bbenchoff/Dumb-Badge/Art-Assets/Documentation/CodePage437.png

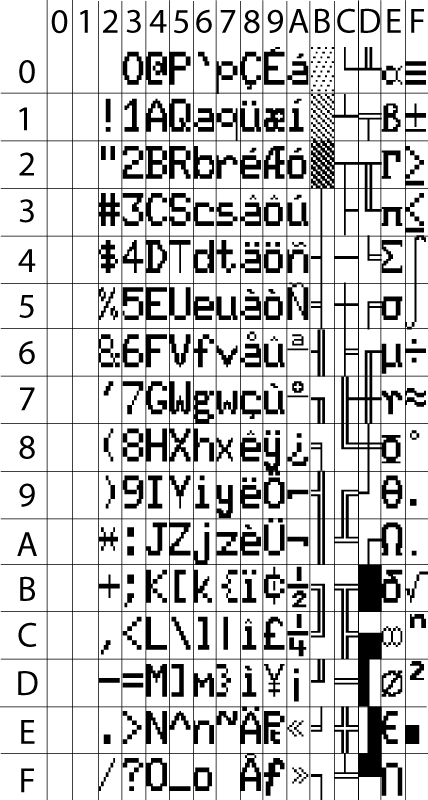
Art-Assets/Documentation/CodePage437.png
