bbenchoff/Dumb-Badge/Art-Assets/Documentation/GraphicRenditionDataStructure.png

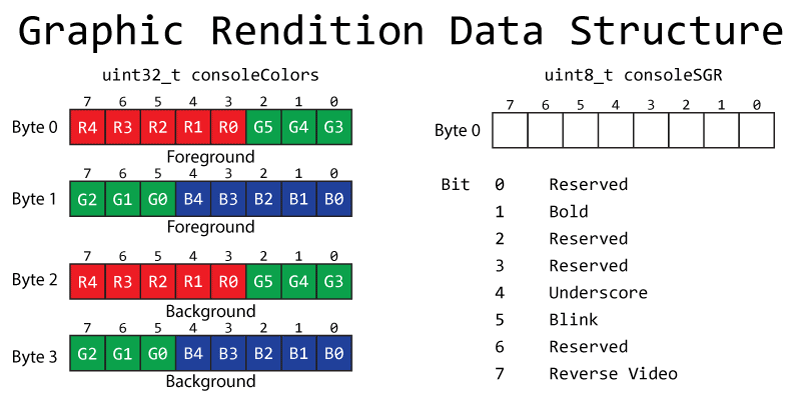
Art-Assets/Documentation/GraphicRenditionDataStructure.png
