bbenchoff/Dumb-Badge/Art-Assets/Documentation/PiHeader.png

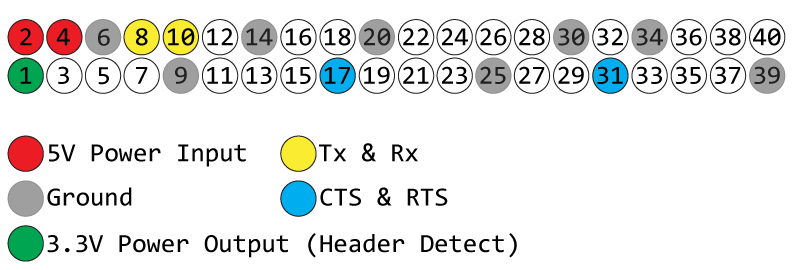
Art-Assets/Documentation/PiHeader.png
