bbenchoff/Dumb-Badge/Art-Assets/Documentation/StateMachine.png

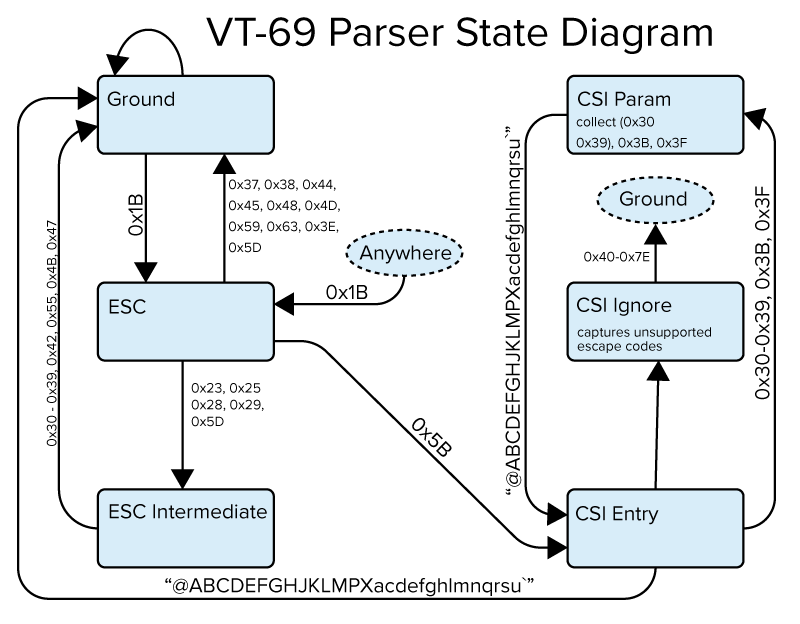
Art-Assets/Documentation/StateMachine.png
