bbenchoff/Dumb-Badge/Art-Assets/Font/CodePage_437.bmp

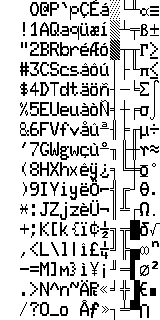
Art-Assets/Font/CodePage_437.bmp
