bbenchoff/Dumb-Badge/Art-Assets/Large Render.png

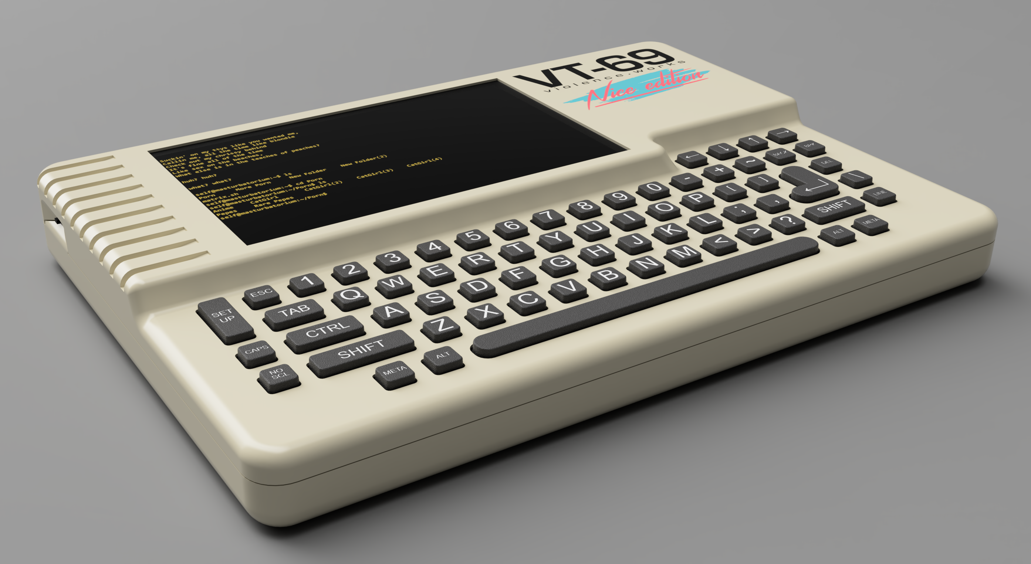
Art-Assets/Large Render.png
