bbenchoff/Dumb-Badge/Art-Assets/Model Decals/ClearConsole.png

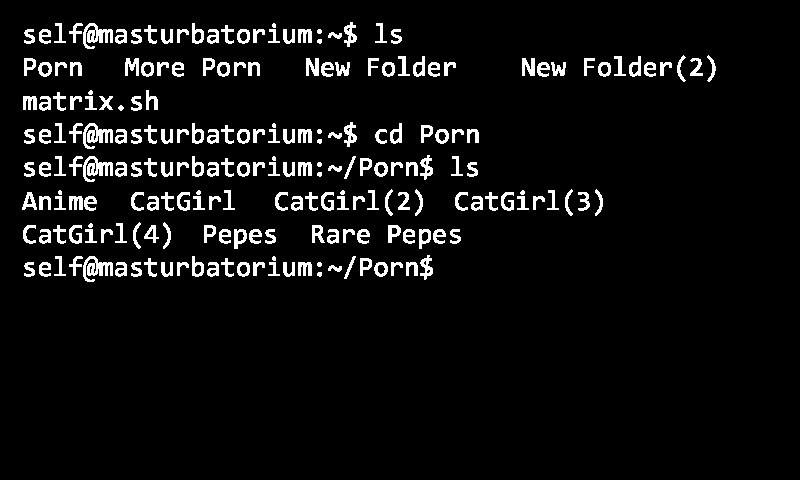
Art-Assets/Model Decals/ClearConsole.png
