bbenchoff/Dumb-Badge/Art-Assets/Model Decals/ClearConsole_flipped.png

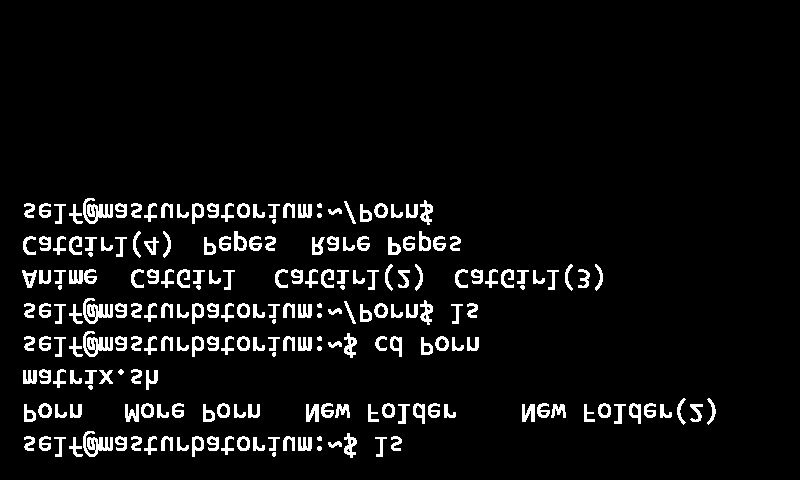
Art-Assets/Model Decals/ClearConsole_flipped.png
