bbenchoff/Dumb-Badge/Art-Assets/Model Decals/Console.png

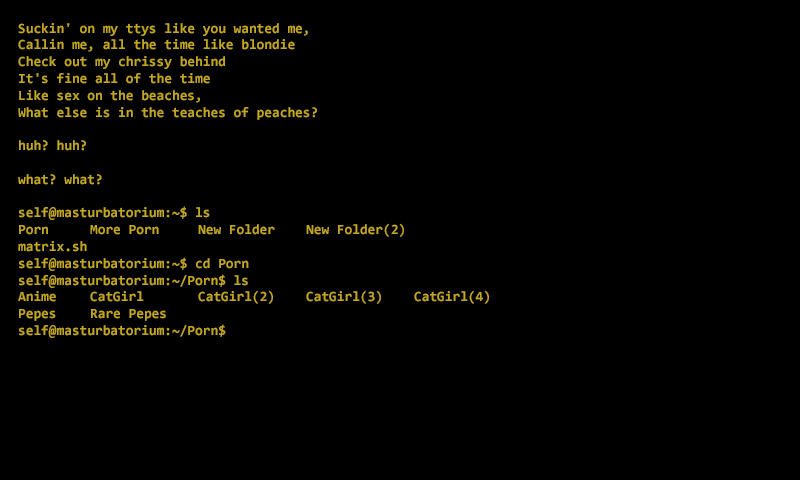
Art-Assets/Model Decals/Console.png
