bbenchoff/Dumb-Badge/Art-Assets/Model Decals/Console_flipped.png

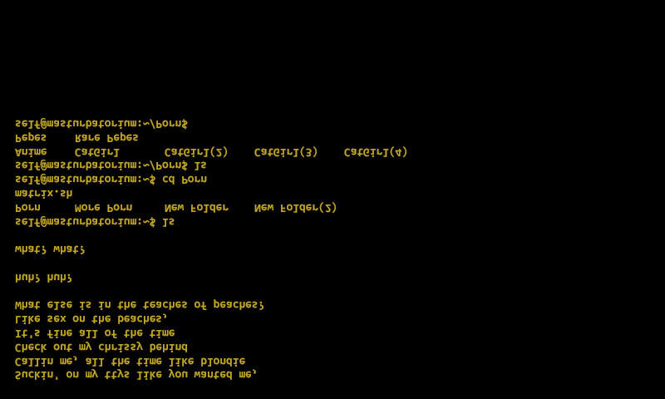
Art-Assets/Model Decals/Console_flipped.png
