bbenchoff/Dumb-Badge/Art-Assets/Model Decals/ConsoleGreen.png

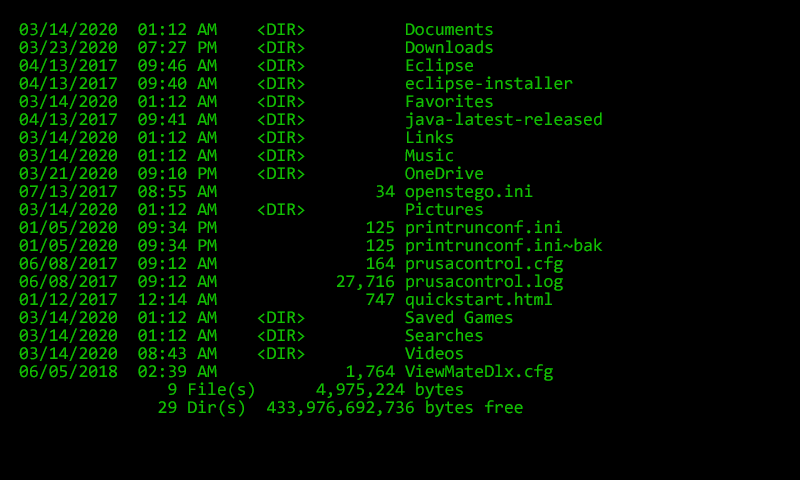
Art-Assets/Model Decals/ConsoleGreen.png
