bbenchoff/Dumb-Badge/Art-Assets/Model Decals/ConsoleGreen_flipped.png

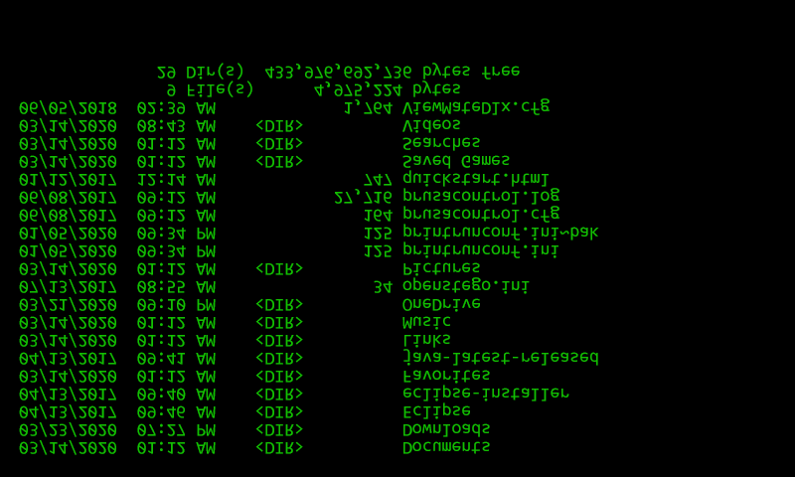
Art-Assets/Model Decals/ConsoleGreen_flipped.png
