bbenchoff/Dumb-Badge/Art-Assets/Model Decals/ConsoleWhite.png

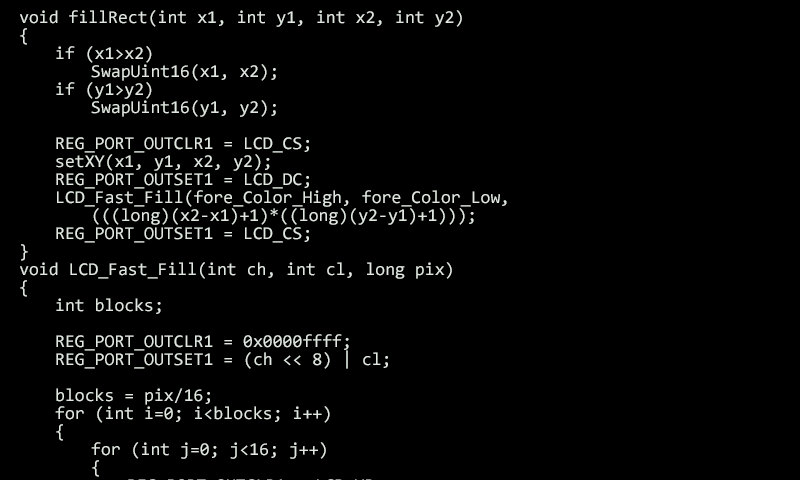
Art-Assets/Model Decals/ConsoleWhite.png
