bbenchoff/Dumb-Badge/Art-Assets/Model Decals/ConsoleWhite_flipped.png

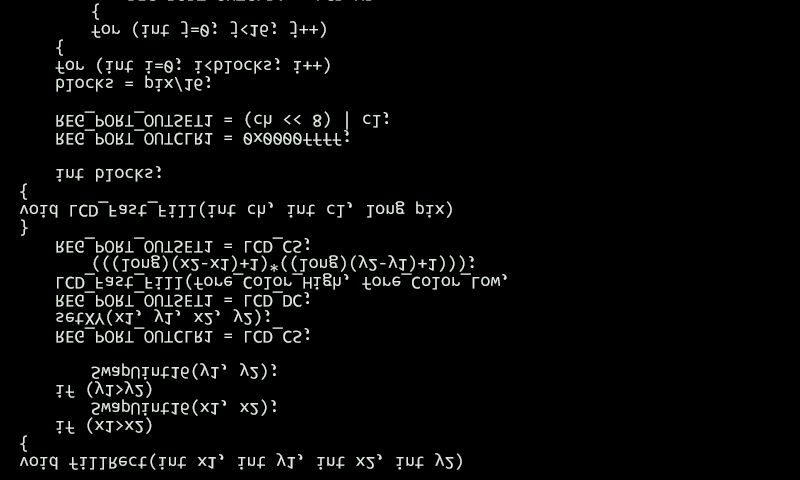
Art-Assets/Model Decals/ConsoleWhite_flipped.png
