bbenchoff/Dumb-Badge/Art-Assets/Model Decals/NiceEdition.png

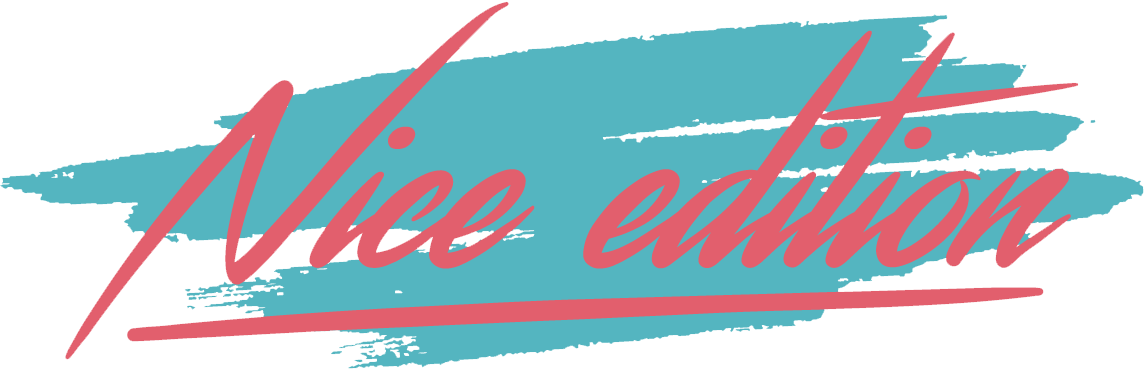
Art-Assets/Model Decals/NiceEdition.png
