bbenchoff/Dumb-Badge/Art-Assets/Model Decals/NiceEdition_flipped.png

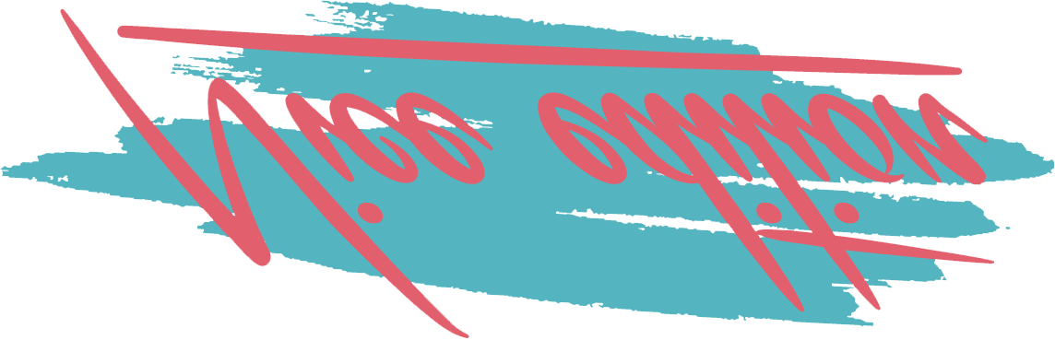
Art-Assets/Model Decals/NiceEdition_flipped.png
