bbenchoff/Dumb-Badge/Art-Assets/Model Decals/TechNews.png

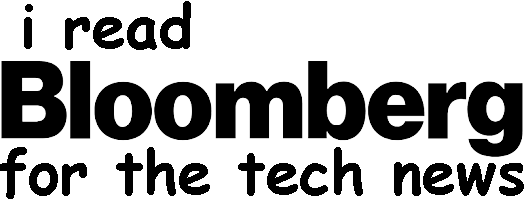
Art-Assets/Model Decals/TechNews.png
