bbenchoff/Dumb-Badge/Art-Assets/Model Decals/TechNews_flipped.png

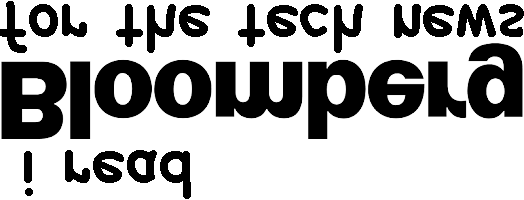
Art-Assets/Model Decals/TechNews_flipped.png
