bbenchoff/Dumb-Badge/Art-Assets/Model Decals/Transparent.png

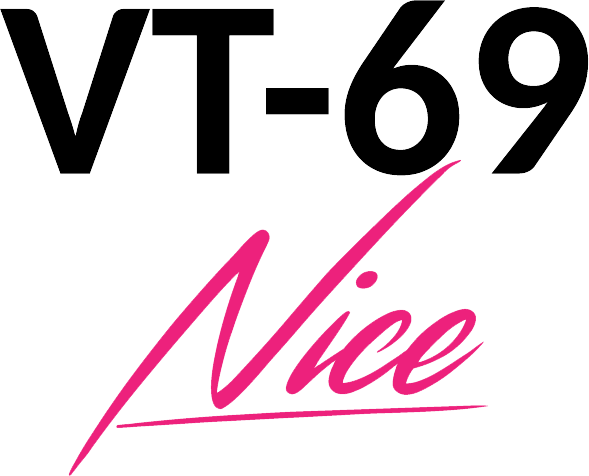
Art-Assets/Model Decals/Transparent.png
