bbenchoff/Dumb-Badge/Art-Assets/Model Decals/VT69Decal.png

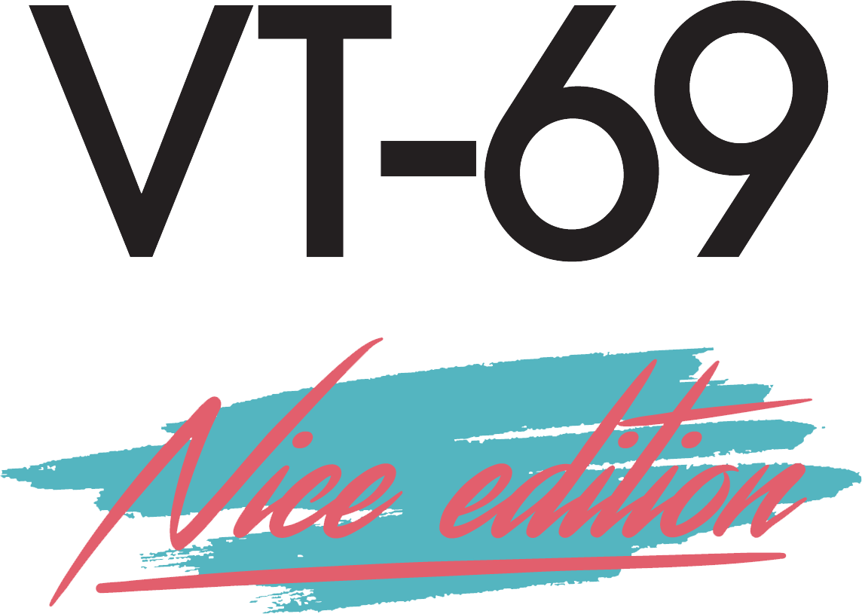
Art-Assets/Model Decals/VT69Decal.png
