bbenchoff/Dumb-Badge/Art-Assets/Model Decals/VT69Decal_flipped.png

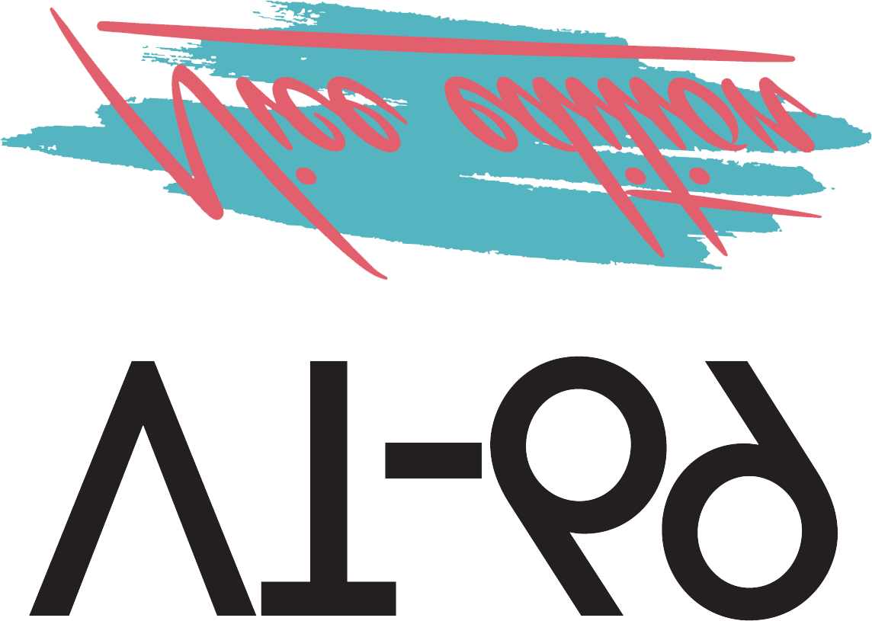
Art-Assets/Model Decals/VT69Decal_flipped.png
