bbenchoff/Dumb-Badge/Art-Assets/Model Decals/VT69DumbTerm.png

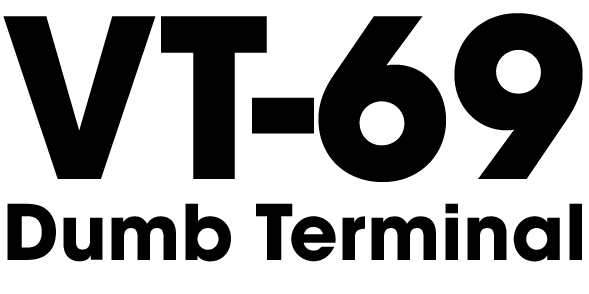
Art-Assets/Model Decals/VT69DumbTerm.png
