bbenchoff/Dumb-Badge/Art-Assets/Model Decals/VT69DumbTerm_flipped.png

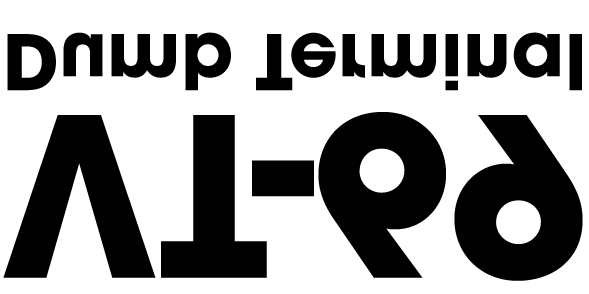
Art-Assets/Model Decals/VT69DumbTerm_flipped.png
