bbenchoff/Dumb-Badge/Art-Assets/Model Decals/VT69DumbTermInverse.png

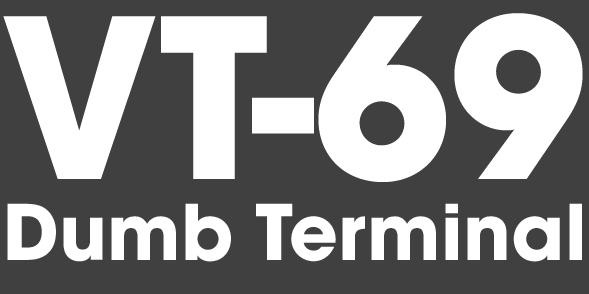
Art-Assets/Model Decals/VT69DumbTermInverse.png
