bbenchoff/Dumb-Badge/Art-Assets/Model Decals/VT69DumbTermInverse_flipped.png

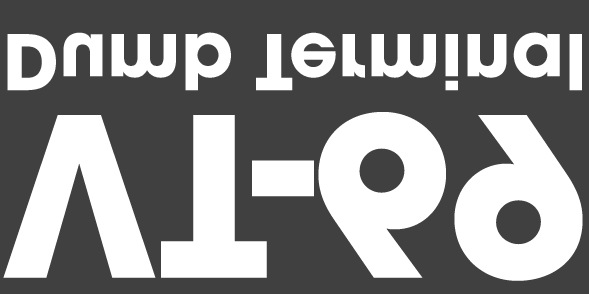
Art-Assets/Model Decals/VT69DumbTermInverse_flipped.png
