bbenchoff/Dumb-Badge/Art-Assets/Model Decals/VT69DumbTermWhite.png

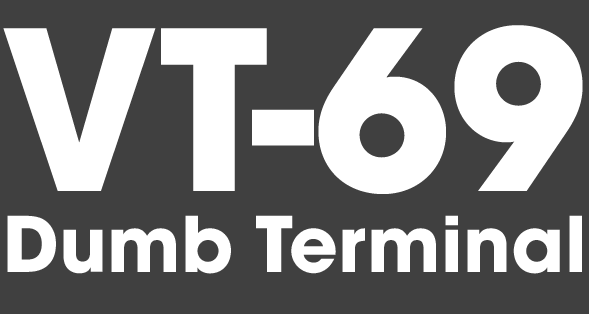
Art-Assets/Model Decals/VT69DumbTermWhite.png
