bbenchoff/Dumb-Badge/Art-Assets/Model Decals/VT69DumbTermWhite_flipped.png

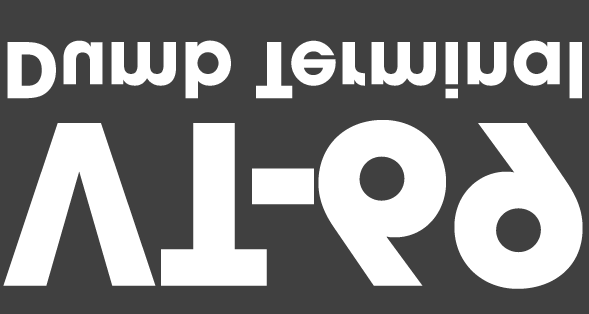
Art-Assets/Model Decals/VT69DumbTermWhite_flipped.png
