bbenchoff/Dumb-Badge/Art-Assets/Model Decals/VT69Nice.png

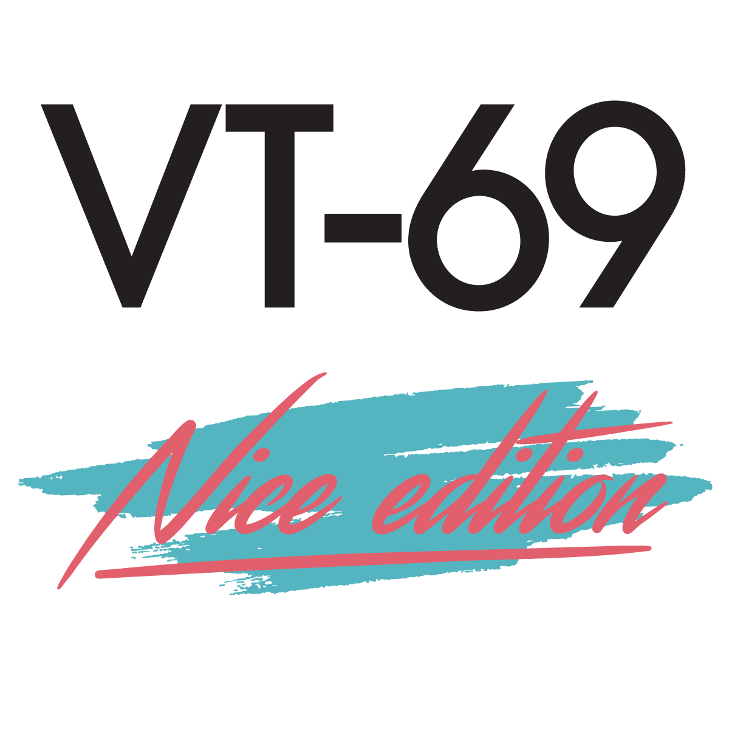
Art-Assets/Model Decals/VT69Nice.png
