bbenchoff/Dumb-Badge/Art-Assets/Model Decals/VT69NiceEditionLong.png

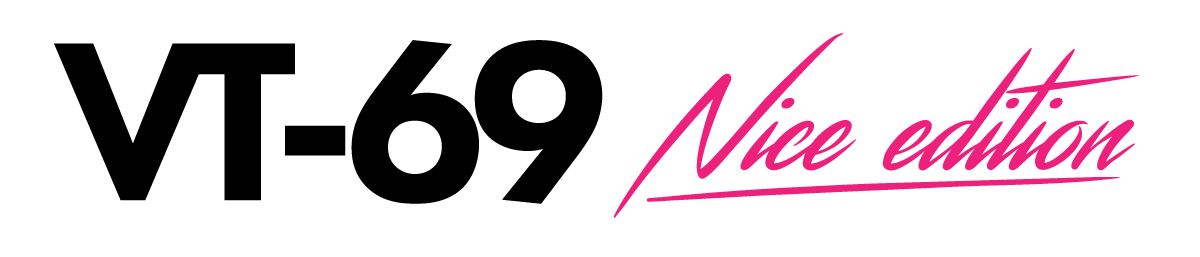
Art-Assets/Model Decals/VT69NiceEditionLong.png
