bbenchoff/Dumb-Badge/Art-Assets/Model Decals/VT69NiceEditionLongTall.png

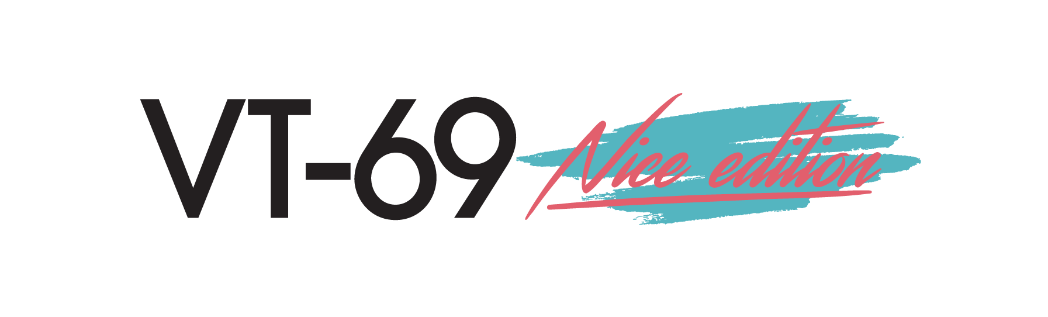
Art-Assets/Model Decals/VT69NiceEditionLongTall.png
