bbenchoff/Dumb-Badge/Art-Assets/Model Decals/VT69NiceEurostyle.png

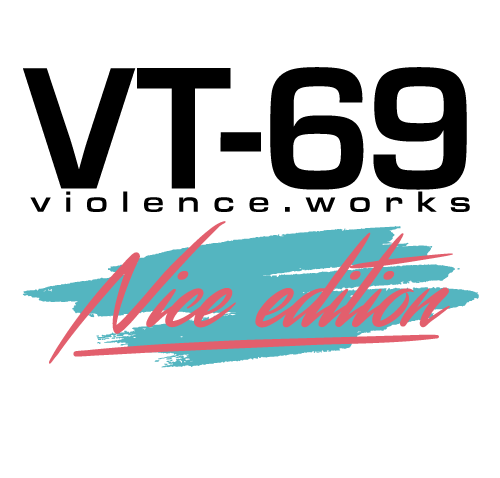
Art-Assets/Model Decals/VT69NiceEurostyle.png
