bbenchoff/Dumb-Badge/Art-Assets/Model Decals/VT69NiceEurostyle_flipped.png

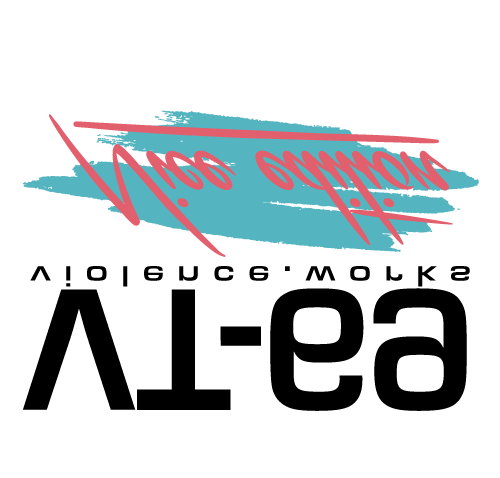
Art-Assets/Model Decals/VT69NiceEurostyle_flipped.png
