bbenchoff/Dumb-Badge/Art-Assets/Model Decals/VT69NiceSquare.png

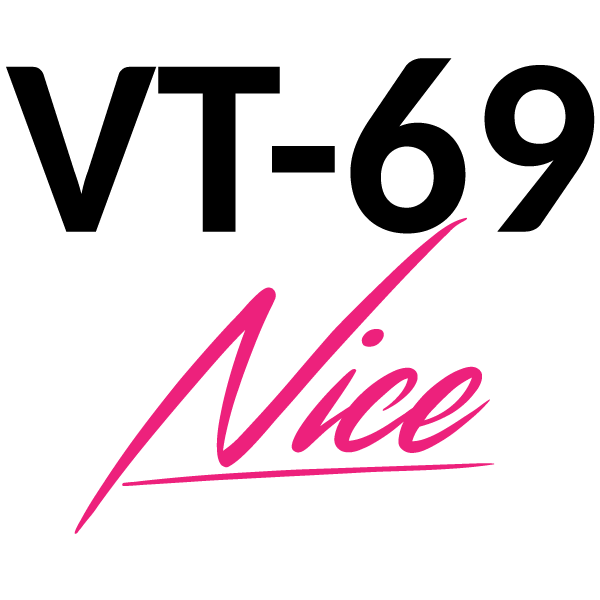
Art-Assets/Model Decals/VT69NiceSquare.png
