bbenchoff/Dumb-Badge/Art-Assets/RandomGraphics/ComfortablyDumb.png

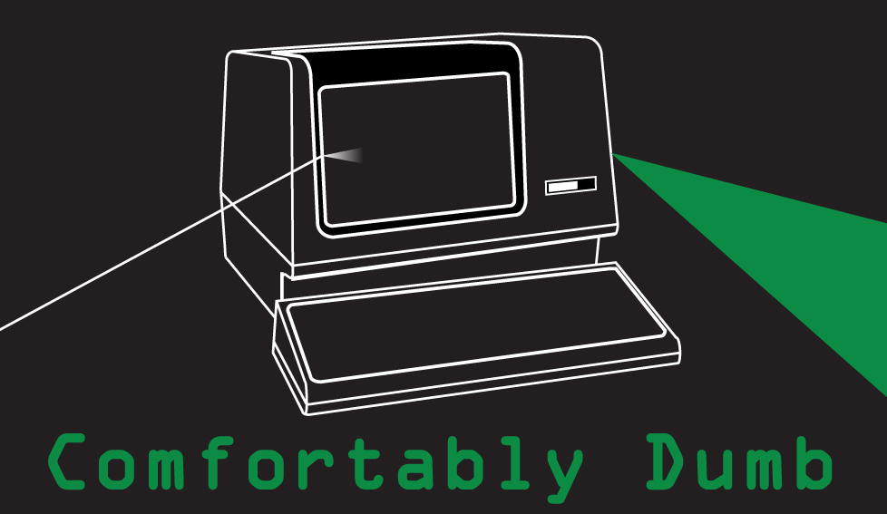
Art-Assets/RandomGraphics/ComfortablyDumb.png
