bbenchoff/Dumb-Badge/Art-Assets/RandomGraphics/Dick S/DickSPNG.png

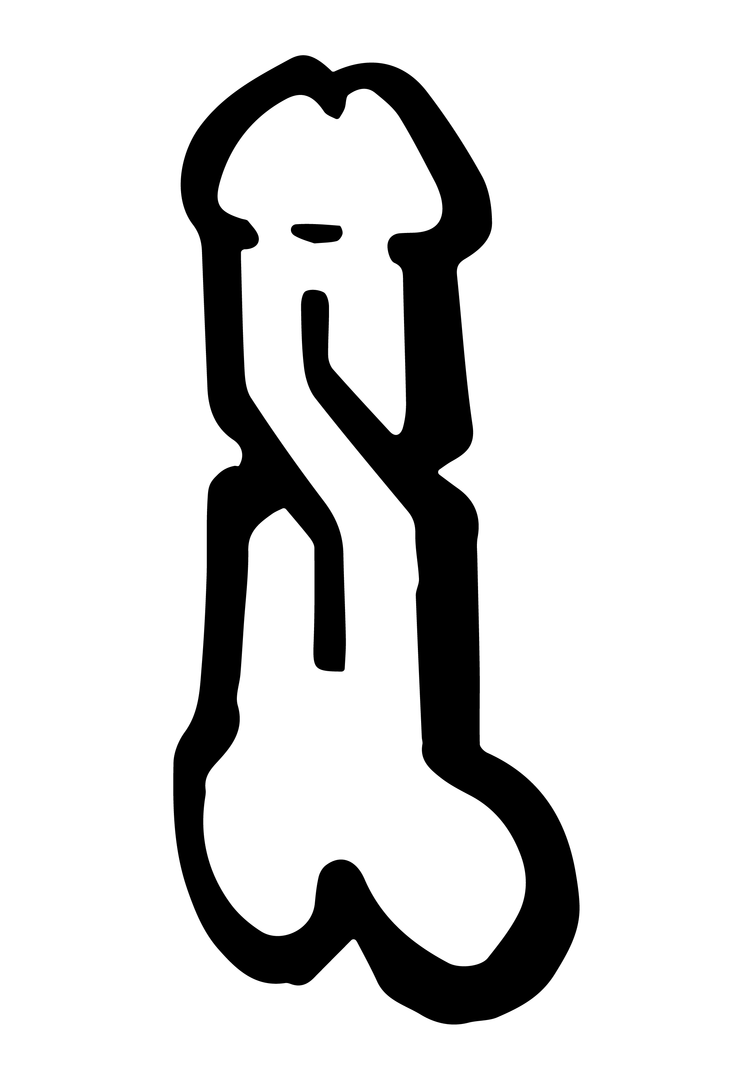
Art-Assets/RandomGraphics/Dick S/DickSPNG.png
