bbenchoff/Dumb-Badge/Art-Assets/RandomGraphics/KillAllTheWhiteMan/KillAll800x480.png

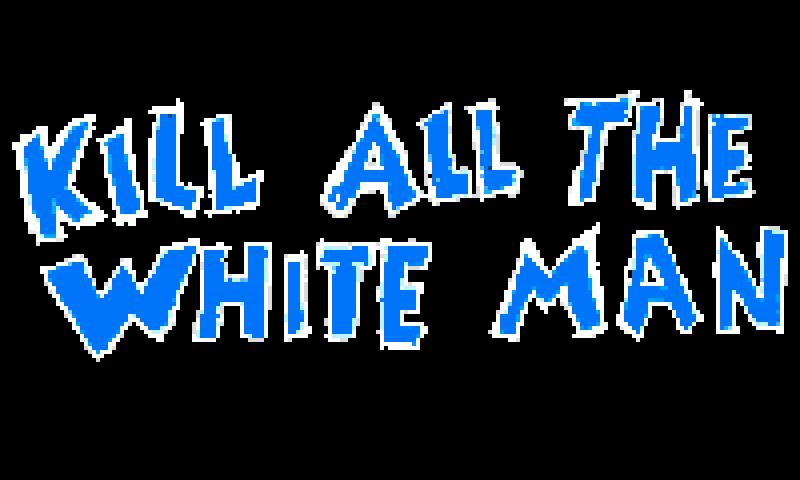
Art-Assets/RandomGraphics/KillAllTheWhiteMan/KillAll800x480.png
