bbenchoff/Dumb-Badge/Art-Assets/RandomGraphics/KillAllTheWhiteMan/KillAll.png

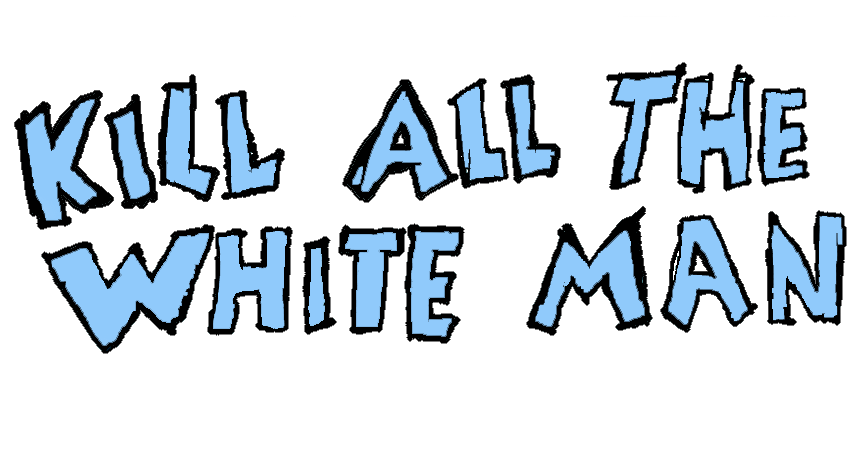
Art-Assets/RandomGraphics/KillAllTheWhiteMan/KillAll.png
