bbenchoff/Dumb-Badge/Art-Assets/RandomGraphics/MechDrawing/Drawing.png

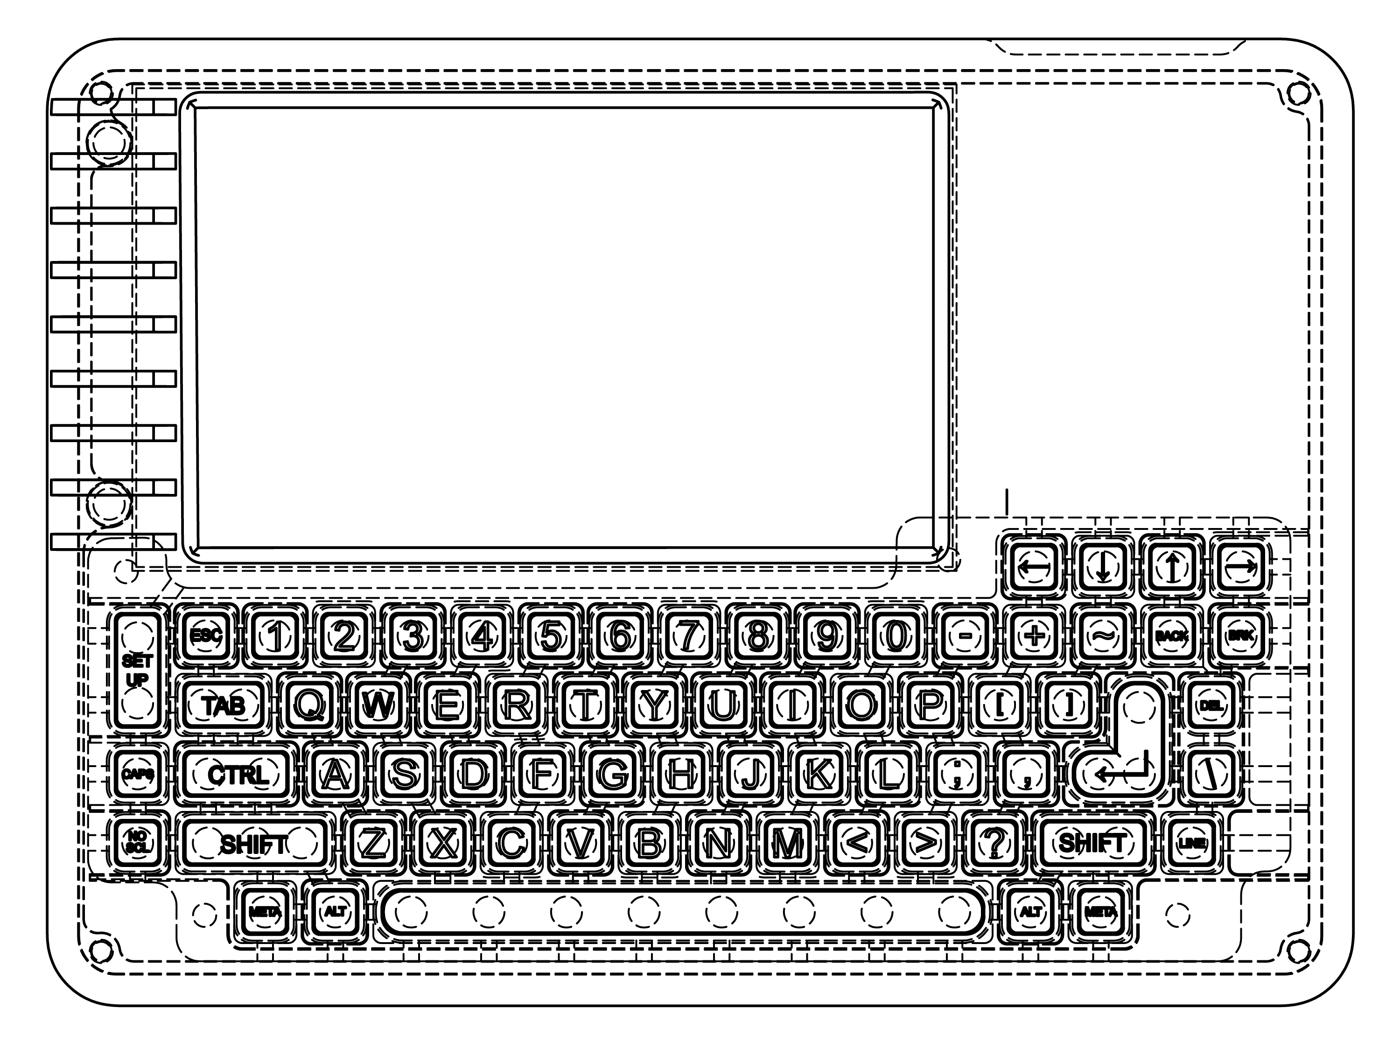
Art-Assets/RandomGraphics/MechDrawing/Drawing.png
