bbenchoff/Dumb-Badge/Art-Assets/RandomGraphics/MechDrawing/DrawingInvert.png

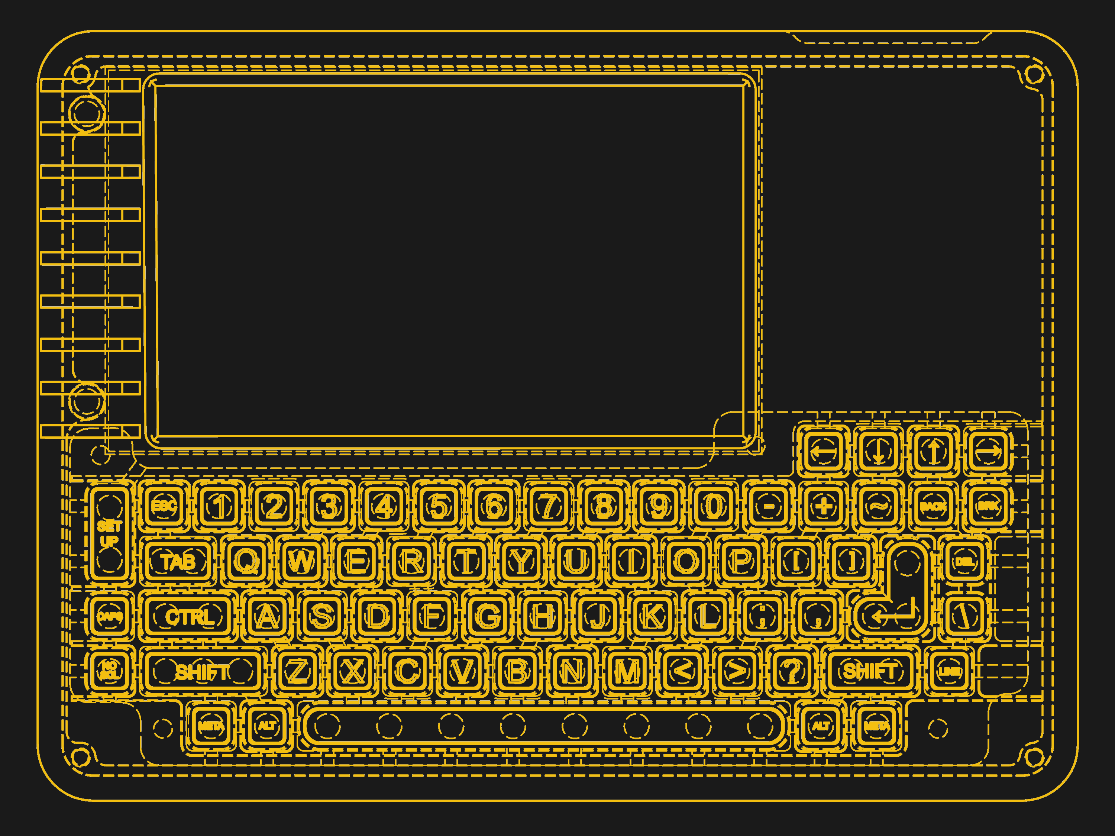
Art-Assets/RandomGraphics/MechDrawing/DrawingInvert.png
