bbenchoff/Dumb-Badge/Art-Assets/RandomGraphics/MechDrawing/YellowTransparentMechDrawing.png

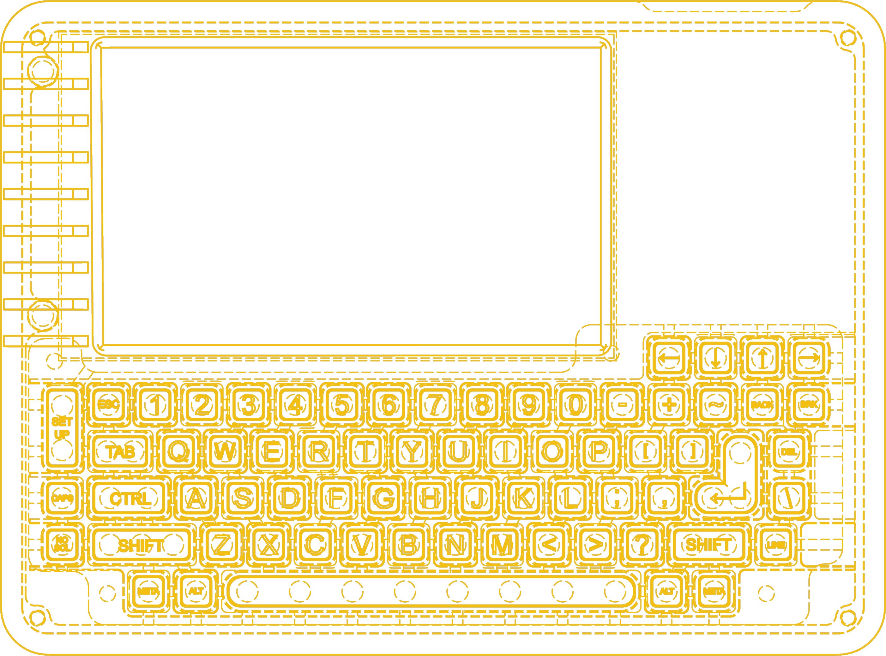
Art-Assets/RandomGraphics/MechDrawing/YellowTransparentMechDrawing.png
