bbenchoff/Dumb-Badge/Art-Assets/RandomGraphics/NiceTTYs/NiceTTYs.png

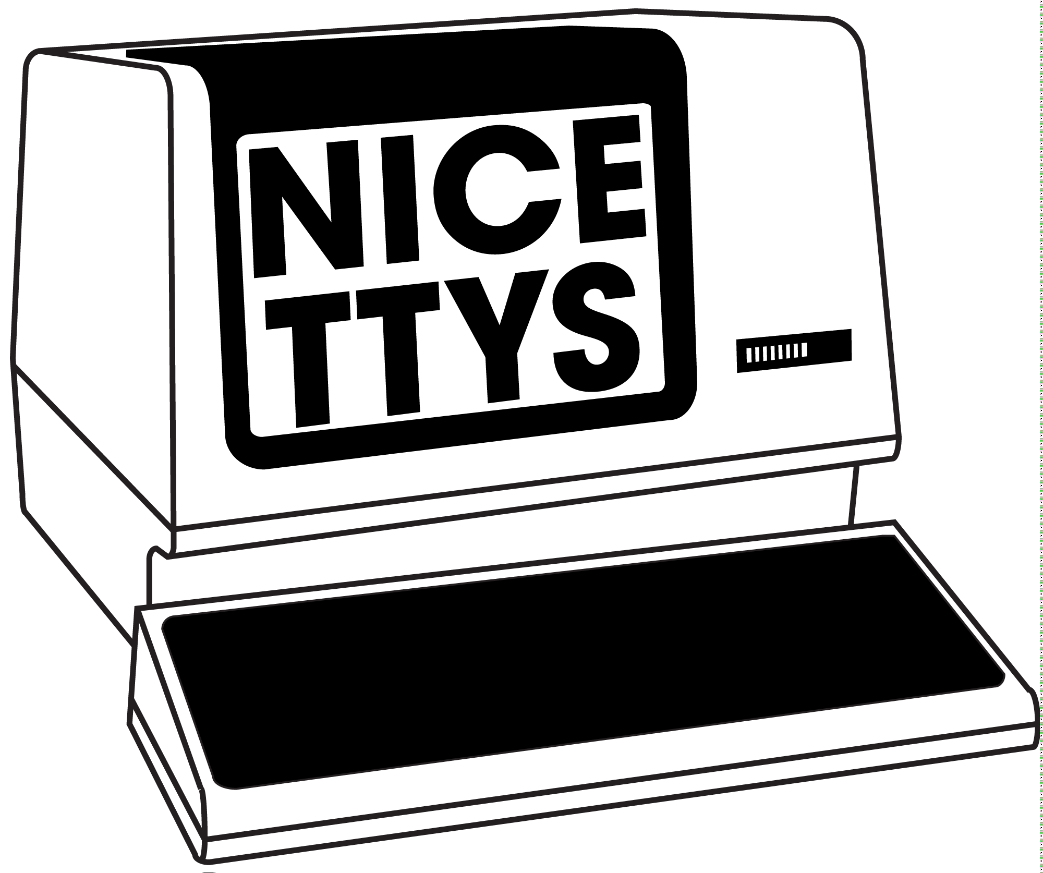
Art-Assets/RandomGraphics/NiceTTYs/NiceTTYs.png
