bbenchoff/Dumb-Badge/Art-Assets/RandomGraphics/reference/Album Covers where guitars are spaceships/51t4X-C2m3L.jpg

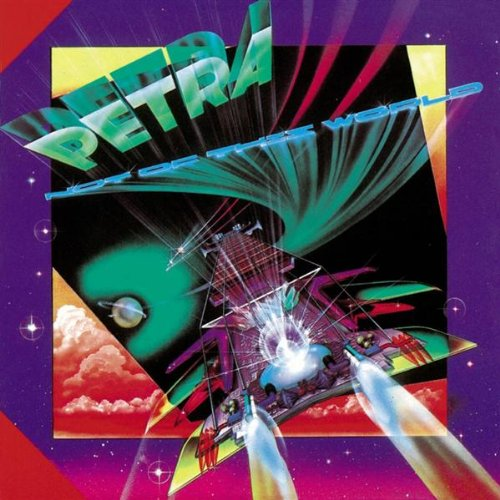
Art-Assets/RandomGraphics/reference/Album Covers where guitars are spaceships/51t4X-C2m3L.jpg
