bbenchoff/Dumb-Badge/Art-Assets/RandomGraphics/reference/Album Covers where guitars are spaceships/740739_10151165755966707_379962912_o.jpg

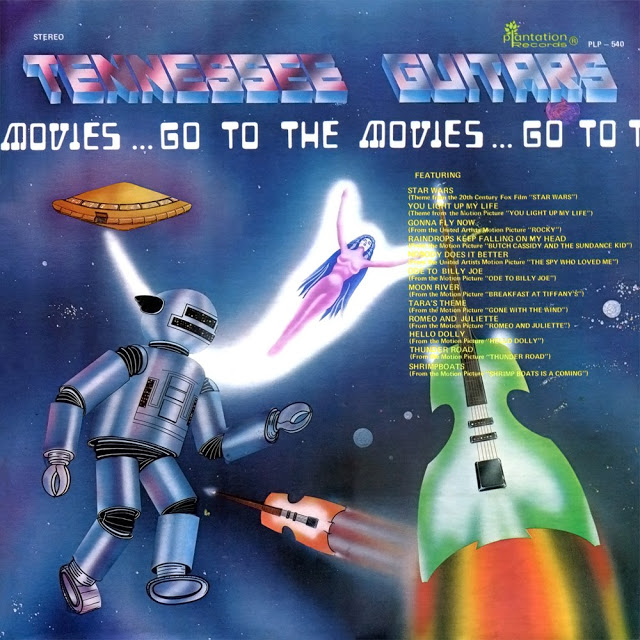
Art-Assets/RandomGraphics/reference/Album Covers where guitars are spaceships/740739_10151165755966707_379962912_o.jpg
