bbenchoff/Dumb-Badge/Art-Assets/RandomGraphics/reference/Album Covers where guitars are spaceships/cbf672cb8266beb2027a6619fb71dfe7.1000x1000x1.jpg

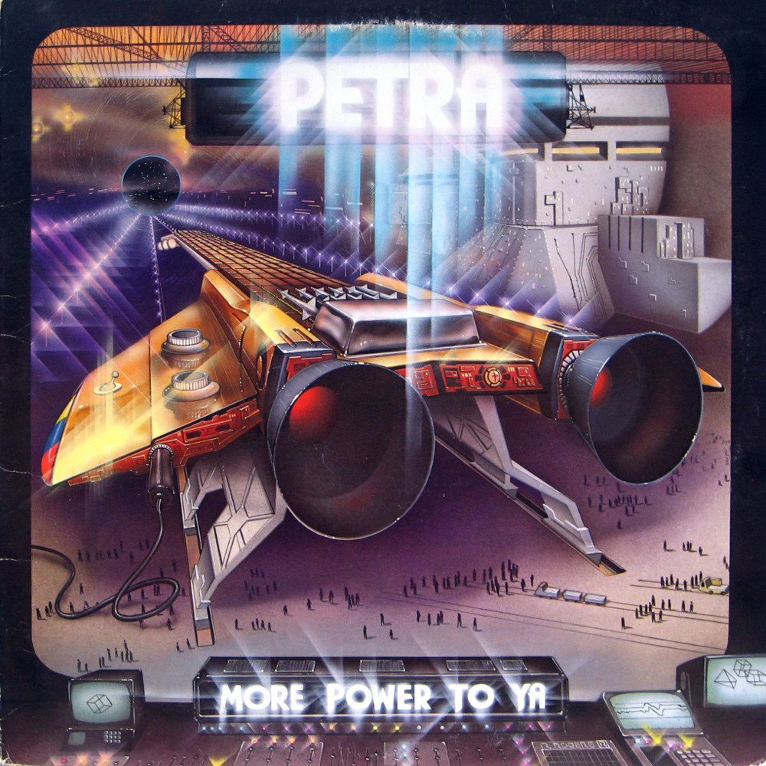
Art-Assets/RandomGraphics/reference/Album Covers where guitars are spaceships/cbf672cb8266beb2027a6619fb71dfe7.1000x1000x1.jpg
