bbenchoff/Dumb-Badge/Art-Assets/RandomGraphics/reference/Album Covers where guitars are spaceships/CNINJA.jpg

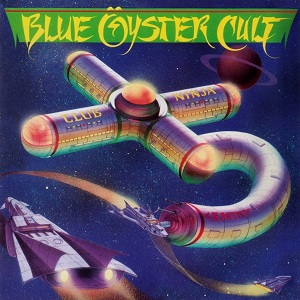
Art-Assets/RandomGraphics/reference/Album Covers where guitars are spaceships/CNINJA.jpg
