bbenchoff/Dumb-Badge/Art-Assets/RandomGraphics/reference/Album Covers where guitars are spaceships/MI0000687644.jpg

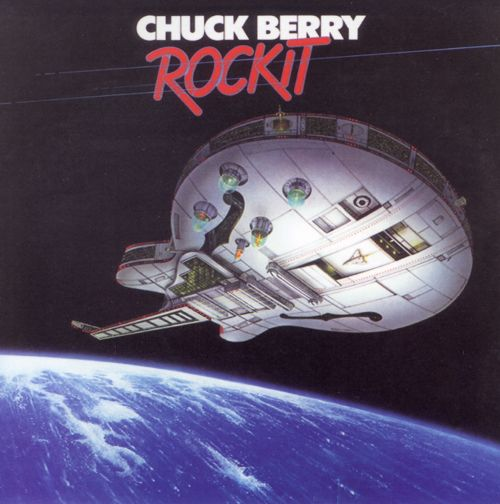
Art-Assets/RandomGraphics/reference/Album Covers where guitars are spaceships/MI0000687644.jpg
