bbenchoff/Dumb-Badge/Art-Assets/RandomGraphics/reference/Album Covers where guitars are spaceships/MI0001766384.jpg

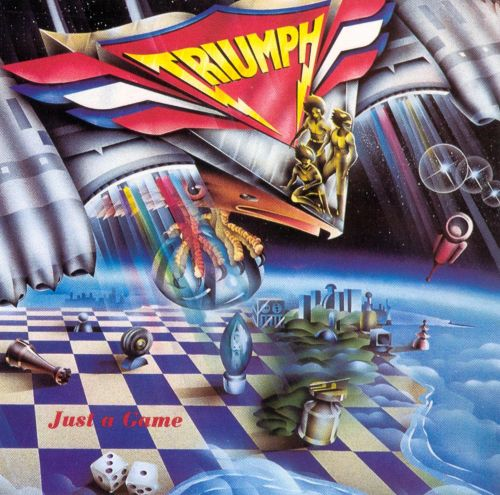
Art-Assets/RandomGraphics/reference/Album Covers where guitars are spaceships/MI0001766384.jpg
