bbenchoff/Dumb-Badge/Art-Assets/RandomGraphics/reference/Album Covers where guitars are spaceships/quartz-against-all-odds-20180325070727.jpg

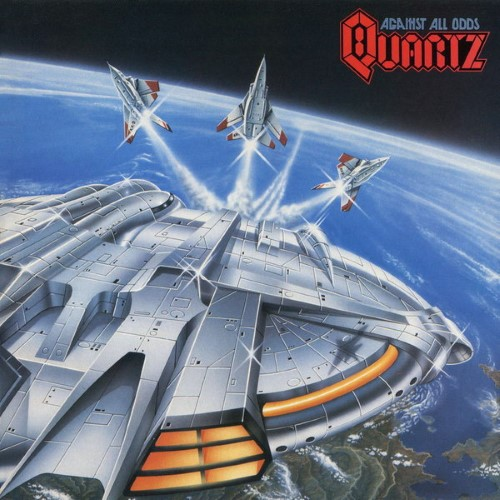
Art-Assets/RandomGraphics/reference/Album Covers where guitars are spaceships/quartz-against-all-odds-20180325070727.jpg
