bbenchoff/Dumb-Badge/Art-Assets/RandomGraphics/reference/Album Covers where guitars are spaceships/R-342681-1356796270-8952.jpeg.jpg

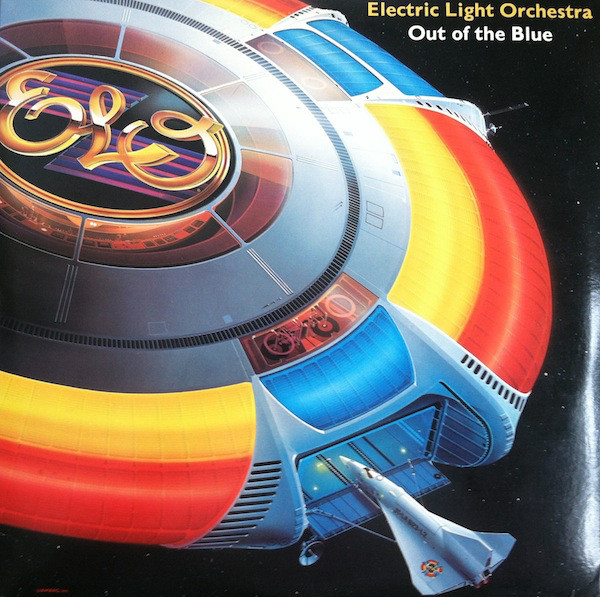
Art-Assets/RandomGraphics/reference/Album Covers where guitars are spaceships/R-342681-1356796270-8952.jpeg.jpg
