bbenchoff/Dumb-Badge/Art-Assets/RandomGraphics/reference/Album Covers where guitars are spaceships/R-543205-1365450873-9314.jpeg.jpg

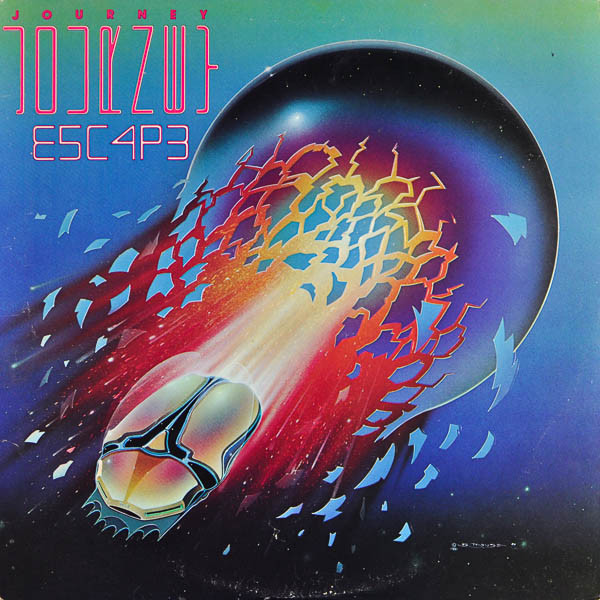
Art-Assets/RandomGraphics/reference/Album Covers where guitars are spaceships/R-543205-1365450873-9314.jpeg.jpg
