bbenchoff/Dumb-Badge/Art-Assets/RandomGraphics/reference/Album Covers where guitars are spaceships/R-1697630-1237652205.jpeg.jpg

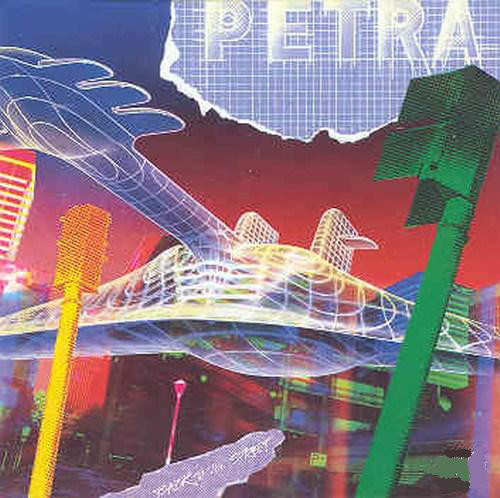
Art-Assets/RandomGraphics/reference/Album Covers where guitars are spaceships/R-1697630-1237652205.jpeg.jpg
