bbenchoff/Dumb-Badge/Art-Assets/RandomGraphics/reference/Album Covers where guitars are spaceships/R-1715578-1274193568.jpeg.jpg

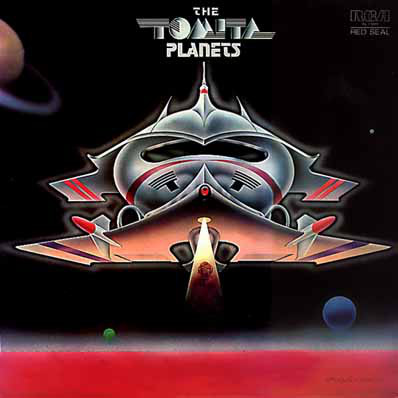
Art-Assets/RandomGraphics/reference/Album Covers where guitars are spaceships/R-1715578-1274193568.jpeg.jpg
