bbenchoff/Dumb-Badge/Art-Assets/RandomGraphics/SoloJazz/1.png

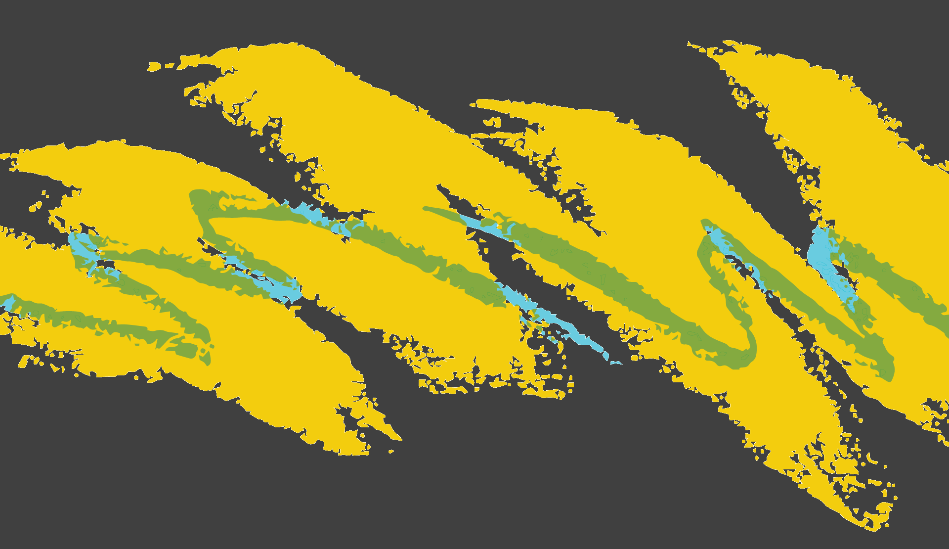
Art-Assets/RandomGraphics/SoloJazz/1.png
