bbenchoff/Dumb-Badge/Art-Assets/RandomGraphics/SoloJazz/2.png

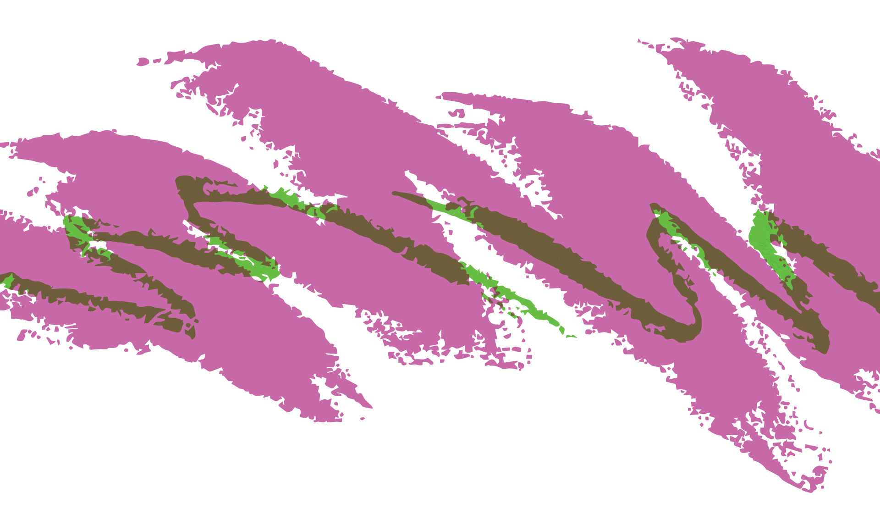
Art-Assets/RandomGraphics/SoloJazz/2.png
