bbenchoff/Dumb-Badge/Art-Assets/RandomGraphics/SoloJazz/lol-art.png

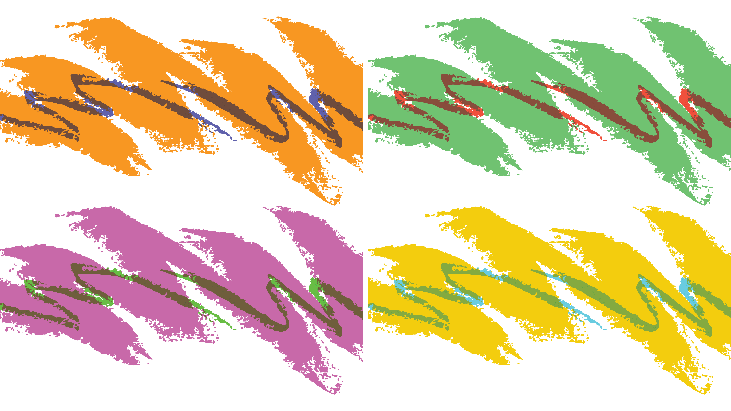
Art-Assets/RandomGraphics/SoloJazz/lol-art.png
