bbenchoff/Dumb-Badge/Art-Assets/RandomGraphics/SpiritOf89/SpiritOf89.png

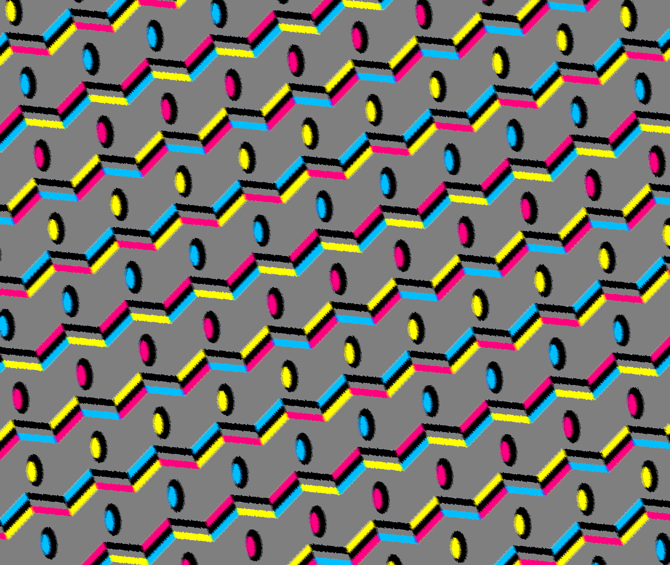
Art-Assets/RandomGraphics/SpiritOf89/SpiritOf89.png
