bbenchoff/Dumb-Badge/Art-Assets/RandomGraphics/SpiritOf89/SpiritOf89small.png

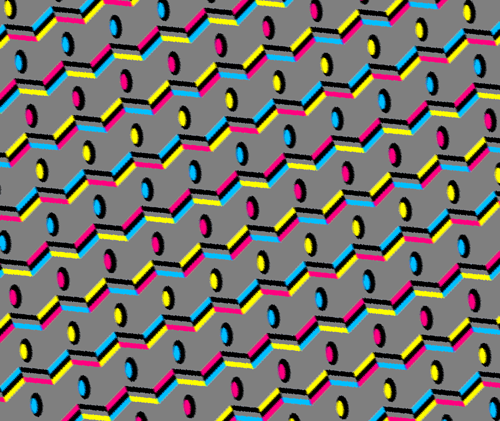
Art-Assets/RandomGraphics/SpiritOf89/SpiritOf89small.png
