bbenchoff/Dumb-Badge/Art-Assets/RandomGraphics/SusanKare/BigSadTerm.png

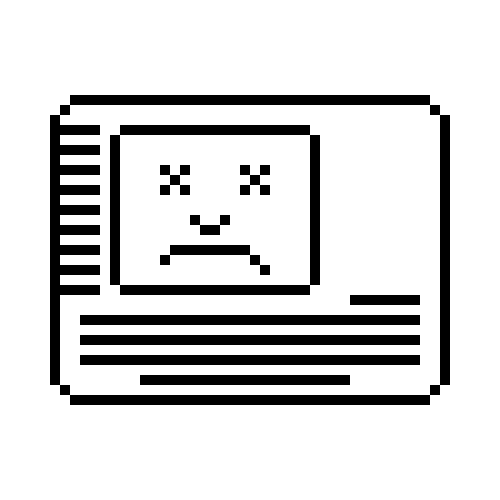
Art-Assets/RandomGraphics/SusanKare/BigSadTerm.png
