bbenchoff/Dumb-Badge/Art-Assets/RandomGraphics/SusanKare/BigVersion.png

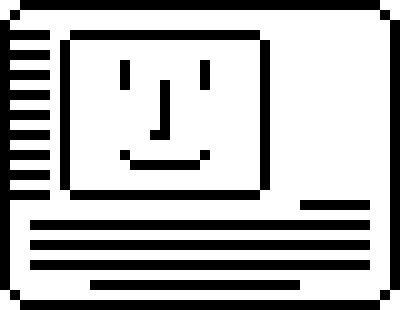
Art-Assets/RandomGraphics/SusanKare/BigVersion.png
