bbenchoff/Dumb-Badge/Art-Assets/RandomGraphics/SusanKare/SadTerm.png

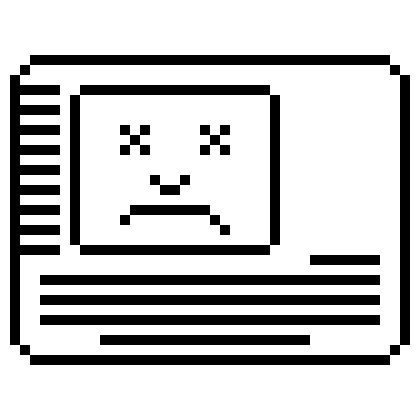
Art-Assets/RandomGraphics/SusanKare/SadTerm.png
