bbenchoff/Dumb-Badge/Art-Assets/RandomGraphics/Terminal/blankTerm.png

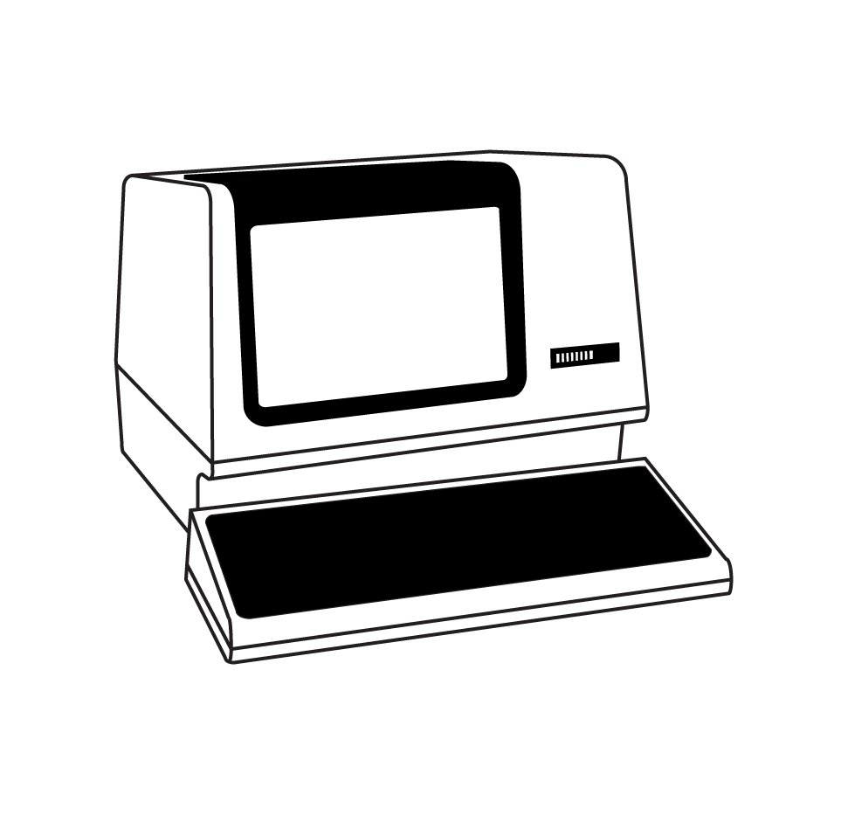
Art-Assets/RandomGraphics/Terminal/blankTerm.png
