bbenchoff/Dumb-Badge/Art-Assets/RandomGraphics/ToeJam/ToejamAndEarl.png

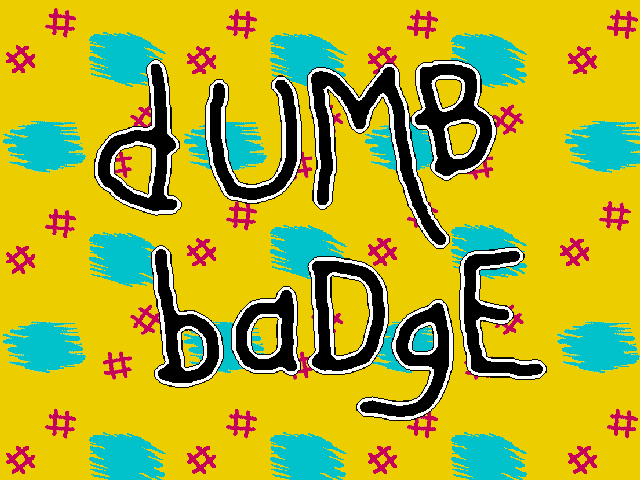
Art-Assets/RandomGraphics/ToeJam/ToejamAndEarl.png
