bbenchoff/Dumb-Badge/Art-Assets/RandomGraphics/ToeJam/ToejamAndEarlWide.png

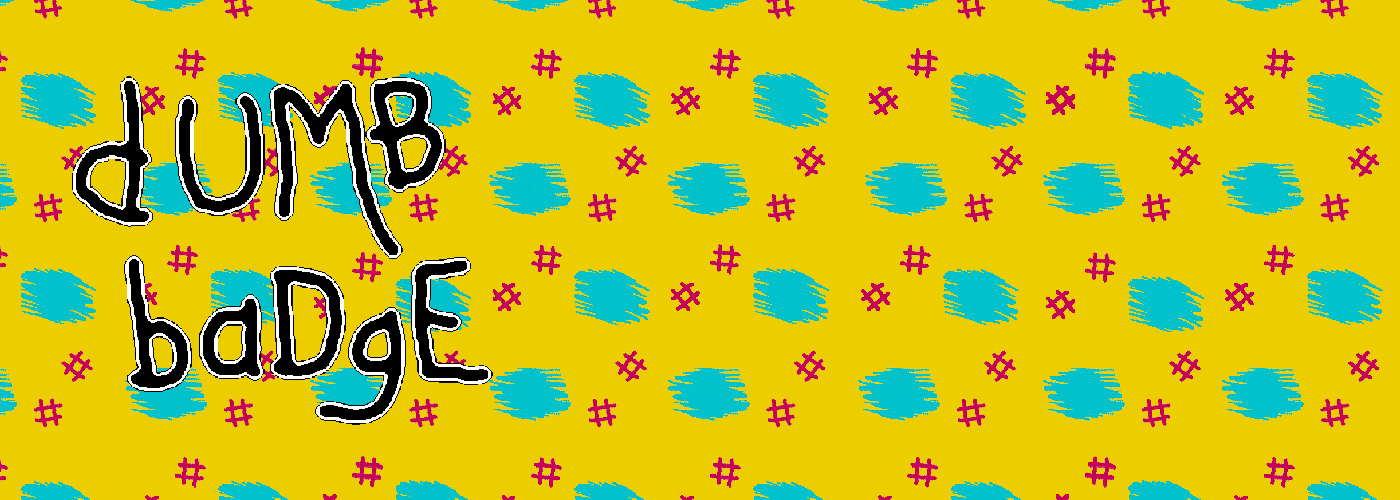
Art-Assets/RandomGraphics/ToeJam/ToejamAndEarlWide.png
