bbenchoff/Dumb-Badge/Art-Assets/RandomGraphics/Vaporwave.png

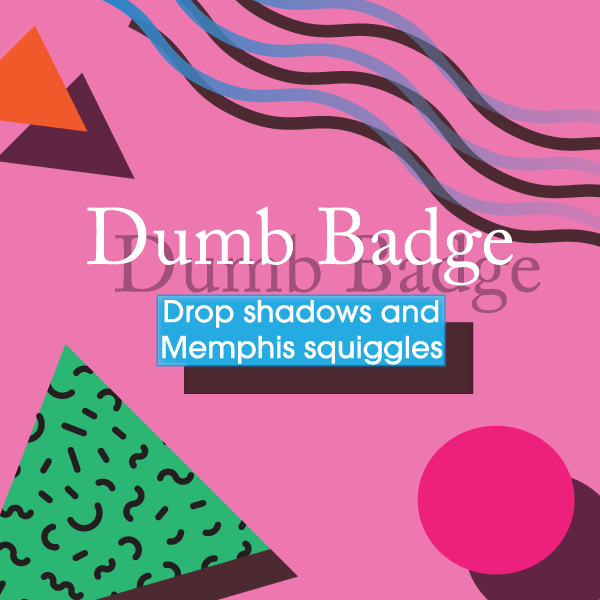
Art-Assets/RandomGraphics/Vaporwave.png
