bbenchoff/Dumb-Badge/Docu/CoverExample.png

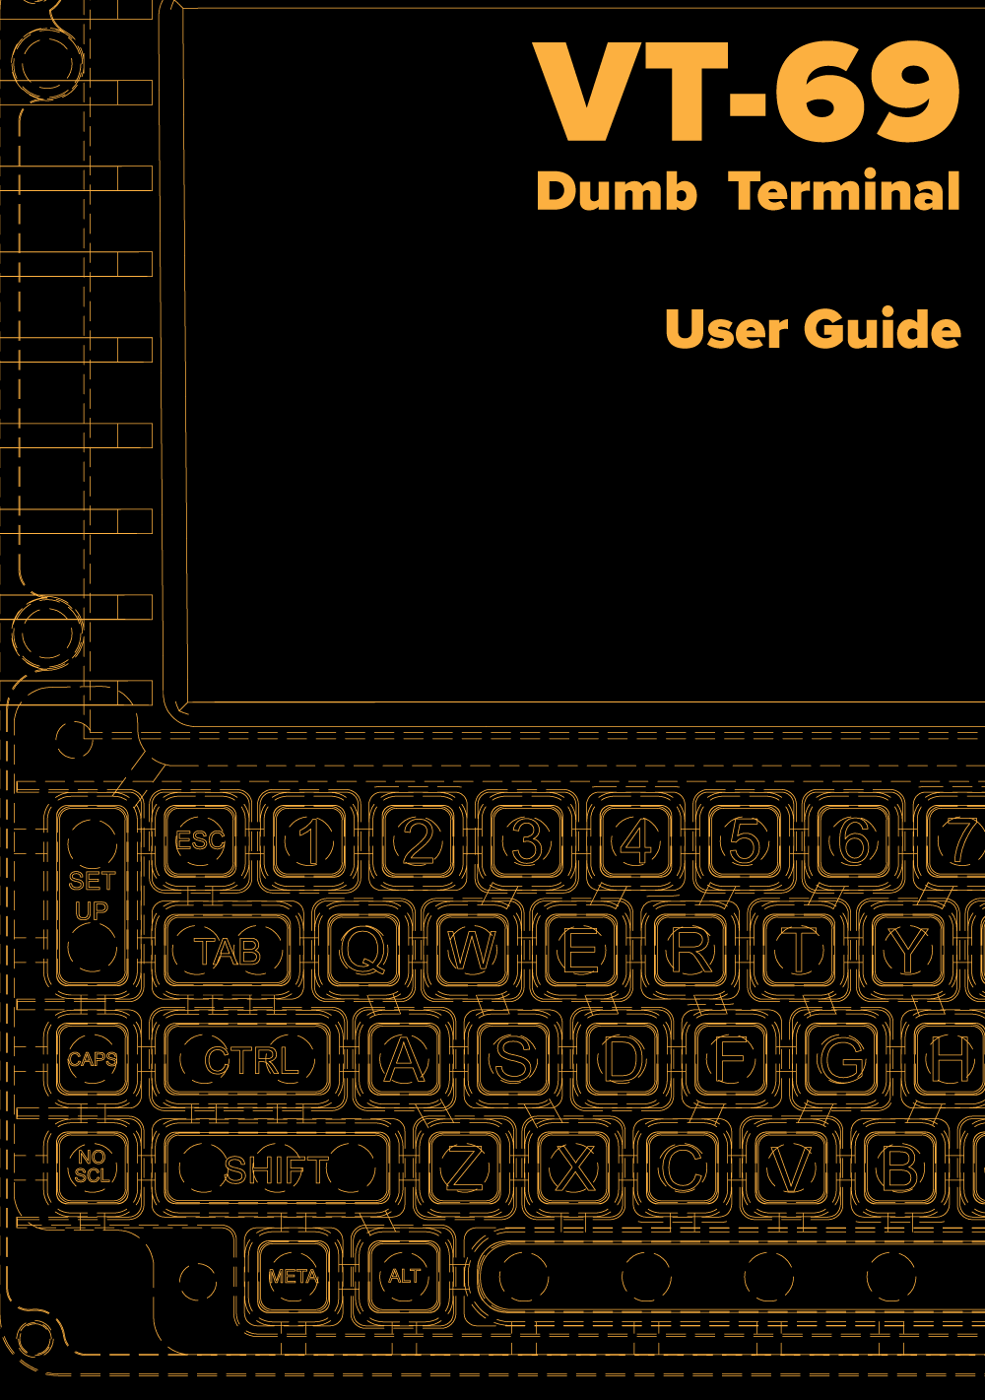
Docu/CoverExample.png
