bbenchoff/Dumb-Badge/Extensions/ESP/BaudBox.bmp

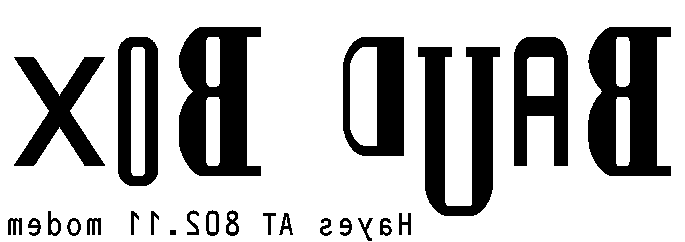
Extensions/ESP/BaudBox.bmp
