bbenchoff/Dumb-Badge/Extensions/ESP/BaudBox.png

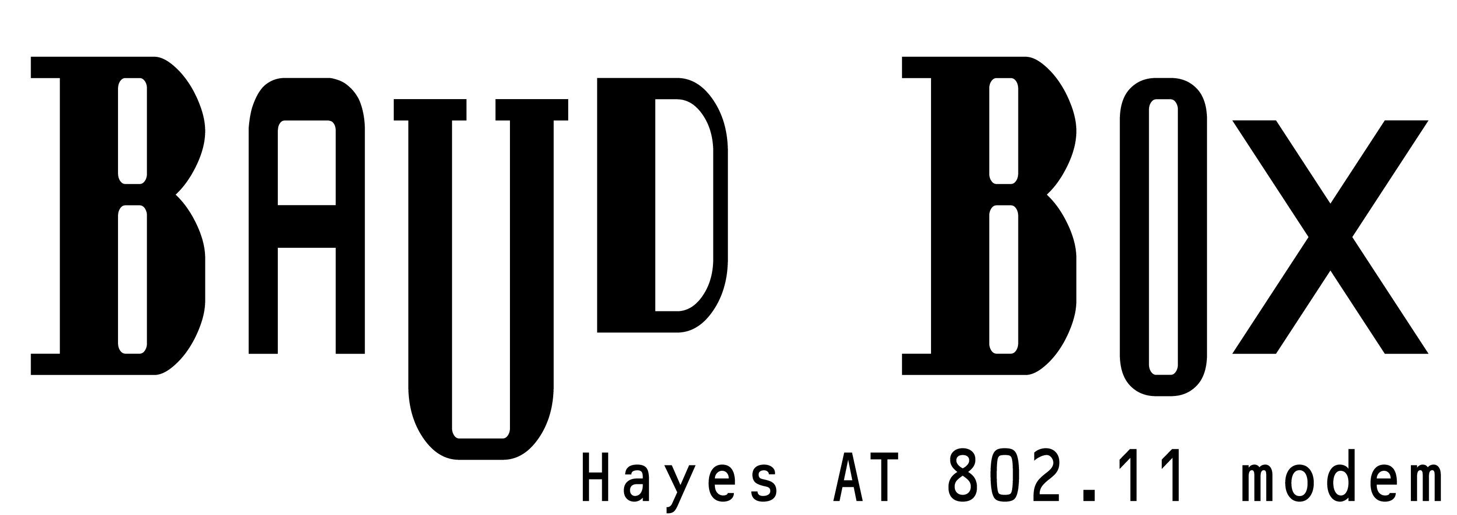
Extensions/ESP/BaudBox.png
