bbenchoff/Dumb-Badge/Extensions/ESP/USTeledildonics.bmp

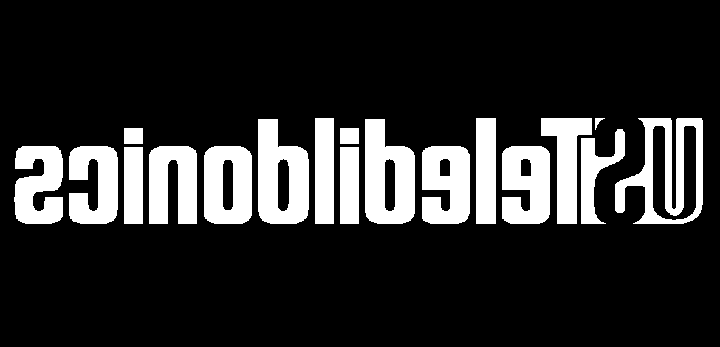
Extensions/ESP/USTeledildonics.bmp
