bbenchoff/Dumb-Badge/Extensions/ESP/USTeledildonics.png

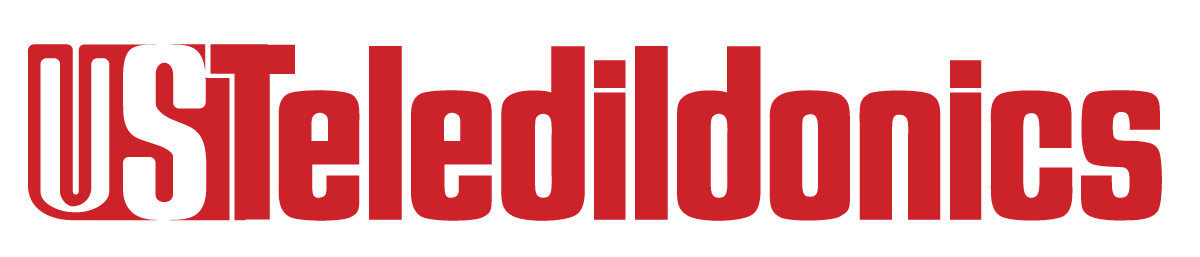
Extensions/ESP/USTeledildonics.png
