bbenchoff/Dumb-Badge/Firmware/DumbBadgeFirmware/src/ASF/sam0/drivers/sercom/sercom_pinout.h

/**
 * \file
 *
 * \brief SAM SERCOM Module Pinout Definitions
 *
 *
 * Copyright (c) 2012-2018 Microchip Technology Inc. and its subsidiaries.
 *
 * \asf_license_start
 *
 * \page License
 *
 * Subject to your compliance with these terms, you may use Microchip
 * software and any derivatives exclusively with Microchip products.
 * It is your responsibility to comply with third party license terms applicable
 * to your use of third party software (including open source software) that
 * may accompany Microchip software.
 *
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
 * \asf_license_stop
 *
 */
/*
 * Support and FAQ: visit <a href="https://www.microchip.com/support/">Microchip Support</a>
 */
#ifndef SERCOM_PINOUT_H_INCLUDED
#define SERCOM_PINOUT_H_INCLUDED

#include <compiler.h>


	/* SERCOM0 */
	#define SERCOM0_PAD0_DEFAULT      PINMUX_PA04D_SERCOM0_PAD0
	#define SERCOM0_PAD1_DEFAULT      PINMUX_PA05D_SERCOM0_PAD1
	#define SERCOM0_PAD2_DEFAULT      PINMUX_PA06D_SERCOM0_PAD2
	#define SERCOM0_PAD3_DEFAULT      PINMUX_PA07D_SERCOM0_PAD3

	/* SERCOM1 */
	#define SERCOM1_PAD0_DEFAULT      PINMUX_PA00D_SERCOM1_PAD0
	#define SERCOM1_PAD1_DEFAULT      PINMUX_PA01D_SERCOM1_PAD1
	#define SERCOM1_PAD2_DEFAULT      PINMUX_PA30D_SERCOM1_PAD2
	#define SERCOM1_PAD3_DEFAULT      PINMUX_PA31D_SERCOM1_PAD3

	/* SERCOM2 */
	#define SERCOM2_PAD0_DEFAULT      PINMUX_PA08D_SERCOM2_PAD0
	#define SERCOM2_PAD1_DEFAULT      PINMUX_PA09D_SERCOM2_PAD1
	#define SERCOM2_PAD2_DEFAULT      PINMUX_PA10D_SERCOM2_PAD2
	#define SERCOM2_PAD3_DEFAULT      PINMUX_PA11D_SERCOM2_PAD3

	/* SERCOM3 */
	#define SERCOM3_PAD0_DEFAULT      PINMUX_PA16D_SERCOM3_PAD0
	#define SERCOM3_PAD1_DEFAULT      PINMUX_PA17D_SERCOM3_PAD1
	#define SERCOM3_PAD2_DEFAULT      PINMUX_PA18D_SERCOM3_PAD2
	#define SERCOM3_PAD3_DEFAULT      PINMUX_PA19D_SERCOM3_PAD3

	/* SERCOM4 */
	#define SERCOM4_PAD0_DEFAULT      PINMUX_PA12D_SERCOM4_PAD0
	#define SERCOM4_PAD1_DEFAULT      PINMUX_PA13D_SERCOM4_PAD1
	#define SERCOM4_PAD2_DEFAULT      PINMUX_PA14D_SERCOM4_PAD2
	#define SERCOM4_PAD3_DEFAULT      PINMUX_PA15D_SERCOM4_PAD3

	/* SERCOM5 */
	#define SERCOM5_PAD0_DEFAULT      PINMUX_PA22D_SERCOM5_PAD0
	#define SERCOM5_PAD1_DEFAULT      PINMUX_PA23D_SERCOM5_PAD1
	#define SERCOM5_PAD2_DEFAULT      PINMUX_PA24D_SERCOM5_PAD2
	#define SERCOM5_PAD3_DEFAULT      PINMUX_PA25D_SERCOM5_PAD3

#endif /* SERCOM_PINOUT_H_INCLUDED */
