bbenchoff/Dumb-Badge/Firmware/DumbBadgeFirmware/src/uart.h

/*
 * uart.h
 *
 * Created: 10/16/2020 3:39:26 PM
 *  Author: bench
 */ 

#ifndef UART_H	
#define UART_H

void parseRXBuffer(void);
void clearRXBuffer(void);

void sendChar(char character);


#endif /* UART_H */
