bbenchoff/Dumb-Badge/Scripts/serialPrint.py

import serial
import sys
import curses
import time


stdscr = curses.initscr()

file = open(sys.argv[2],"rb")

ser = serial.Serial(sys.argv[1])
stdscr.clear()

stdscr.addstr(sys.argv[2])
stdscr.addstr(" Open ")
stdscr.addstr(ser.name)
stdscr.refresh()

byte=file.read(1)

while byte:

    c = byte
    stdscr.addstr(1,0, "Next Byte: ")
    stdscr.addstr(c)
    stdscr.addstr("  ")
    stdscr.refresh()

                  
    ser.write(byte)
    byte=file.read(1)
    time.sleep(.025)
    
ser.close()
file.close()
